eugenioorosco8/Poncho_IoT_EDU_CIAA_NXP/Software NODO CENTRAL - EDU CIAA/src/sapi_spi.c

/* Copyright 2016, Eric Pernia.
 * All rights reserved.
 *
 * This file is part of CIAA Firmware.
 *
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
 * 3. Neither the name of the copyright holder nor the names of its
 *    contributors may be used to endorse or promote products derived from this
 *    software without specific prior written permission.
 *
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
 */

/*
 * modification history (new versions first)
 * -----------------------------------------------------------
 * 2016-05-02   v0.0.1   ENP   First version
 */

/*==================[inclusions]=============================================*/

#include "sapi_spi.h"
#include "chip.h"

/*==================[macros and definitions]=================================*/

/*==================[internal data declaration]==============================*/

/*==================[internal functions declaration]=========================*/

/*==================[internal data definition]===============================*/

/*==================[external data definition]===============================*/

/*==================[internal functions definition]==========================*/

/*==================[external functions definition]==========================*/

bool_t SPIbegin( spiMap_t spi ){  //MJ- comienzo
   
   bool_t retVal = TRUE;
   
   if( spi == SPI0 ){
      
  		/* Set up clock and power for SSP1 module */
		// Configure SSP SSP1 pins
		Chip_SCU_PinMuxSet(0xf,4, (SCU_MODE_PULLUP | SCU_MODE_FUNC0)); // CLK0
		Chip_SCU_PinMuxSet(0x1, 3, (SCU_MODE_PULLUP | SCU_MODE_INBUFF_EN | SCU_MODE_ZIF_DIS | SCU_MODE_FUNC5)); // MISO1
		Chip_SCU_PinMuxSet(0x1, 4, (SCU_MODE_PULLUP | SCU_MODE_FUNC5)); // MOSI1


      
      // Initialize SSP Peripheral
      Chip_SSP_Init( LPC_SSP1 );
      /*
       * SE INICIA EN MODO MAESTRO
       * MODO 0
       *
       */
      Chip_SSP_Enable( LPC_SSP1 );
      
   } else{
      retVal = FALSE;
   }
   
   return retVal;
}


/*bool_t spiRead( spiMap_t spi, uint8_t* buffer, uint32_t bufferSize ){
   
   bool_t retVal = TRUE;
   
   Chip_SSP_DATA_SETUP_T xferConfig;

	xferConfig.tx_data = NULL;
	xferConfig.tx_cnt  = 0;
	xferConfig.rx_data = buffer;
	xferConfig.rx_cnt  = 0;
	xferConfig.length  = bufferSize;

   if( spi == SPI0 ){
      Chip_SSP_RWFrames_Blocking( LPC_SSP1, &xferConfig );
   } else{
      retVal = FALSE;
   }
   
   return retVal;	
}


bool_t SPITransfer( spiMap_t spi, uint8_t* buffer, uint32_t bufferSize){ //MJ- escritura
   
   bool_t retVal = TRUE;
   
   Chip_SSP_DATA_SETUP_T xferConfig;

	xferConfig.tx_data = buffer;
	xferConfig.tx_cnt  = 0;
	xferConfig.rx_data = NULL;
	xferConfig.rx_cnt  = 0;
	xferConfig.length  = bufferSize;

   if( spi == SPI0 ){
      Chip_SSP_RWFrames_Blocking( LPC_SSP1, &xferConfig );
   } else{
      retVal = FALSE;
   }
   
   return retVal;
}
*/
uint8_t SPITransfer( spiMap_t spi, uint8_t* buffer, uint32_t bufferSize){ //MJ- escritura

	uint8_t bufferrx;


   Chip_SSP_DATA_SETUP_T xferConfig;

	xferConfig.tx_data = buffer;
	xferConfig.tx_cnt  = 0;
	xferConfig.rx_data = &bufferrx;
	xferConfig.rx_cnt  = 0;
	xferConfig.length  = bufferSize;

   if( spi == SPI0 ){
      Chip_SSP_RWFrames_Blocking( LPC_SSP1, &xferConfig );
   } else{
	   bufferrx = FALSE;
   }

   return bufferrx;
}

/*==================[ISR external functions definition]======================*/



/** @} doxygen end group definition */
/*==================[end of file]============================================*/
