eugenioorosco8/Poncho_IoT_EDU_CIAA_NXP/Software NODO CENTRAL - EDU CIAA/inc/WorkApp.h

/*
 * WorkApp.h
 *
 *  Created on: 13 jul. 2018
 *      Author: usuario
 */

#ifndef WORKAPP_H_
#define WORKAPP_H_
#endif /* WORKAPP_H_ */


//--------------------------------Declaradas en este archivo para ser visualizados los arreglos desde el archivo Work_Bluetooth.c


//---------------------------------Funciones para almacenamiento de datos historicos para trabajar con App-----
void Last_Values_App(int* Mediciones);
void Repeat_Values(int* Variable,char j, int value);
void Return_Pointer(int* HumAmbp,int*TempAmbp,int*HumSuelop,int*TempSuelop,int*Horap);
