eugenioorosco8/Poncho_IoT_EDU_CIAA_NXP/Software NODO CENTRAL - EDU CIAA/inc/Work_ADC.h

/*
 * Work_ADC.h
 *
 *  Created on: 1 ago. 2018
 *      Author: usuario
 */

#ifndef WORK_ADC_H_
#define WORK_ADC_H_



#endif /* WORK_ADC_H_ */

#include "chip.h"


void InicializarAdc(uint8_t);

void InicializarIntAdc(void);

uint16_t AdcPolling(void);
