eugenioorosco8/Poncho_IoT_EDU_CIAA_NXP/Software NODO CENTRAL - EDU CIAA/inc/Work_Bomba.h

/*
 * Work_Bomba.h
 *
 *  Created on: 1 ago. 2018
 *      Author: usuario
 */

#ifndef WORK_BOMBA_H_
#define WORK_BOMBA_H_






void Bomba_Riego (int Hum_Suelo, int Nivel_Tanque);



void Ref_Level_App (int Level );


#endif /* WORK_BOMBA_H_ */
